slmnemo/e155snakevga/schematic/snake_vga.kicad_sch

## KiCad design schematic/snake_vga.kicad_sch (2023-12-07, an earlier design)

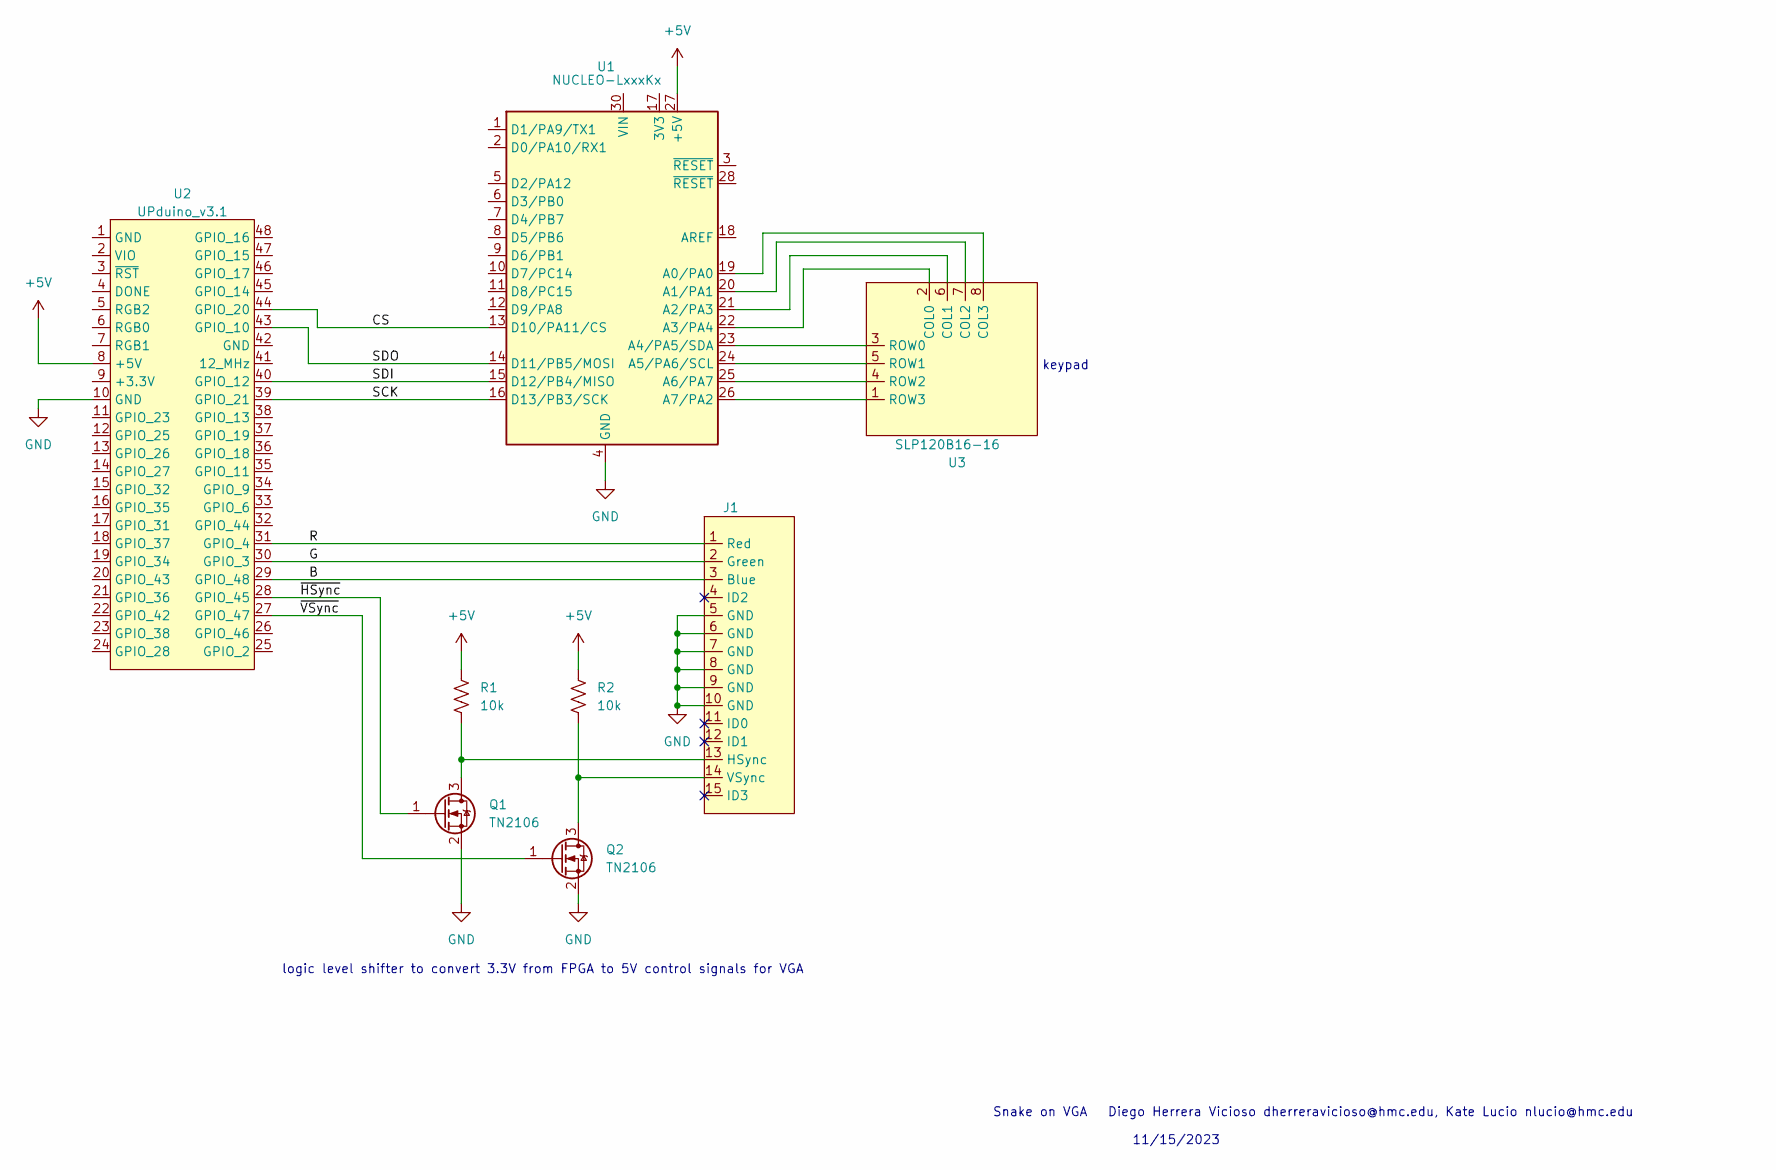
[picture p6: schematic snake_vga.kicad_sch]

Parts:
J1: (no value)
Q1, Q2: TN2106; SOT-23
R1, R2: 10k
U1: NUCLEO-LxxxKx; NUCLEO-32
U2: UPduino_v3.1
U3: SLP120B16-16

Connections:
+5V: R1.1, R2.1, U1.27 (+5V), U2.8 (+5V)
B: J1.3 (Blue), U2.29 (GPIO_48)
CS: U1.13 (D10/PA11/CS), U2.44 (GPIO_20)
G: J1.2 (Green), U2.30 (GPIO_3)
GND: J1.5 (GND), J1.6 (GND), J1.7 (GND), J1.8 (GND), J1.9 (GND), J1.10 (GND), Q1.2 (S), Q2.2 (S), U1.4 (GND), U1.29 (GND), U2.10 (GND)
unnamed: J1.13 (HSync), Q1.3 (D), R1.2
unnamed: J1.14 (VSync), Q2.3 (D), R2.2
unnamed: U1.19 (A0/PA0), U3.8 (COL3)
unnamed: U1.20 (A1/PA1), U3.7 (COL2)
unnamed: U1.21 (A2/PA3), U3.6 (COL1)
unnamed: U1.22 (A3/PA4), U3.2 (COL0)
unnamed: U1.23 (A4/PA5/SDA), U3.3 (ROW0)
unnamed: U1.24 (A5/PA6/SCL), U3.5 (ROW1)
unnamed: U1.25 (A6/PA7), U3.4 (ROW2)
unnamed: U1.26 (A7/PA2), U3.1 (ROW3)
R: J1.1 (Red), U2.31 (GPIO_4)
SCK: U1.16 (D13/PB3/SCK), U2.39 (GPIO_21)
SDI: U1.15 (D12/PB4/MISO), U2.40 (GPIO_12)
SDO: U1.14 (D11/PB5/MOSI), U2.43 (GPIO_10)
~HSync: Q1.1 (G), U2.28 (GPIO_45)
~VSync: Q2.1 (G), U2.27 (GPIO_47)

Notes on the sheet:
logic level shifter to convert 3.3V from FPGA to 5V control signals for VGA
Snake on VGA Diego Herrera Vicioso dherreravicioso@hmc.edu, Kate Lucio nlucio@hmc.edu
11/15/2023
keypad
