slmnemo/e155snakevga/fpga/src/sysclk_pll/misc/sysclk_pll_tmpl.vhd

component sysclk_pll is
    port(
        ref_clk_i: in std_logic;
        rst_n_i: in std_logic;
        outcore_o: out std_logic;
        outglobal_o: out std_logic
    );
end component;

__: sysclk_pll port map(
    ref_clk_i=>,
    rst_n_i=>,
    outcore_o=>,
    outglobal_o=>
);
